NileshAm/ThermoBand-EN1190/Code/test_data/rawData/test_data_plot_2.png

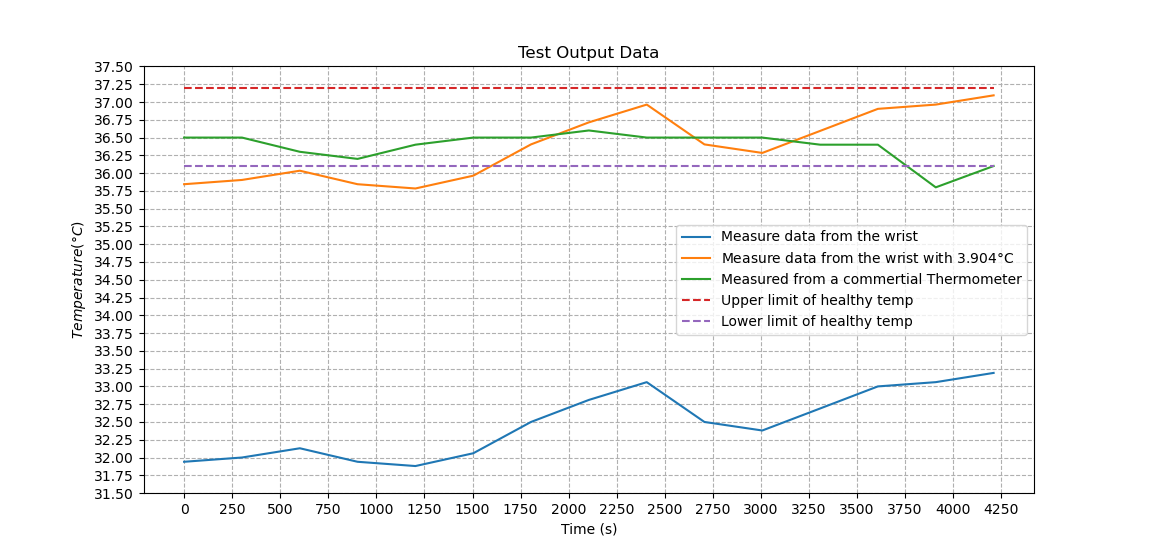
Code/test_data/rawData/test_data_plot_2.png
