NileshAm/ThermoBand-EN1190/Code/main/src/WIFI_Programmer.h

#include <stdint.h>
#ifndef WIFI_PROGRAMMER_H
#define WIFI_PROGRAMMER_H

// Call this from setup() to initialize WiFi and OTA.
// Optional newSSID and newPass parameters allow updating credentials.
void wifiSetupOTA(const char* newSSID = NULL, const char* newPass = NULL, uint8_t LED_PIN=2);

// Call this in your loop() to handle OTA updates.
void otaHandle();

#endif // WIFI_PROGRAMMER_H
